austinscreations/Oxrs-Black/rev 4/oxrs black 004 bottom.jpg

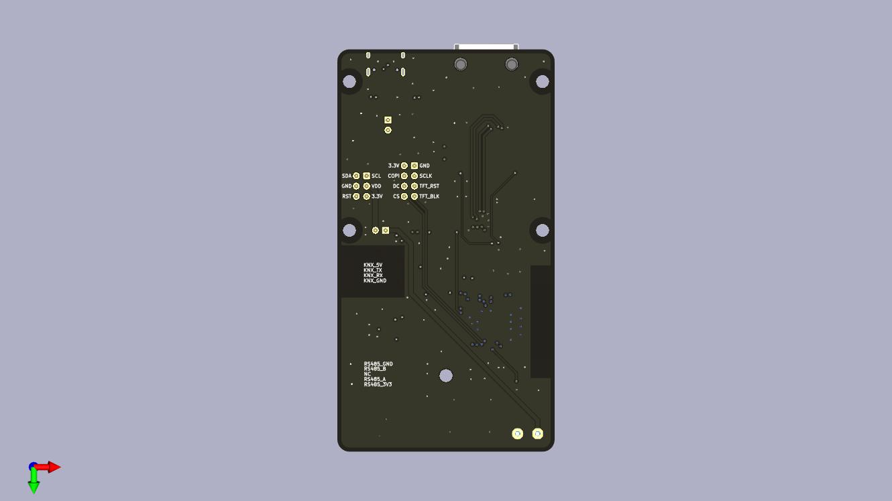
rev 4/oxrs black 004 bottom.jpg
